SP6GK/ADF4351-LO-module/Photos/IMG_20250809_144723.jpg

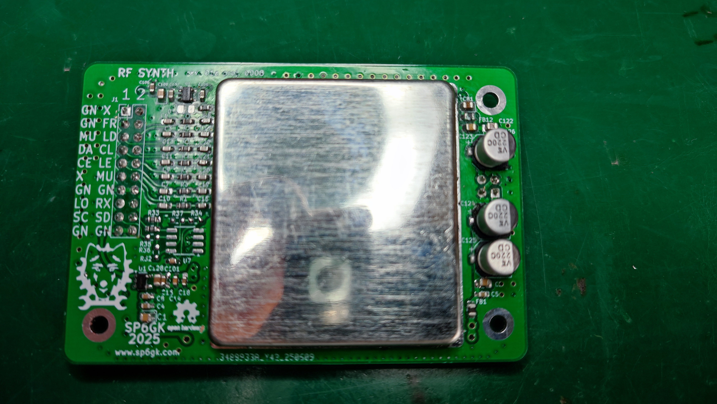
Photos/IMG_20250809_144723.jpg
