SP6GK/ADF4351-LO-module/Verification/Measurements/Adf4351_400MHz_Harmonics.png

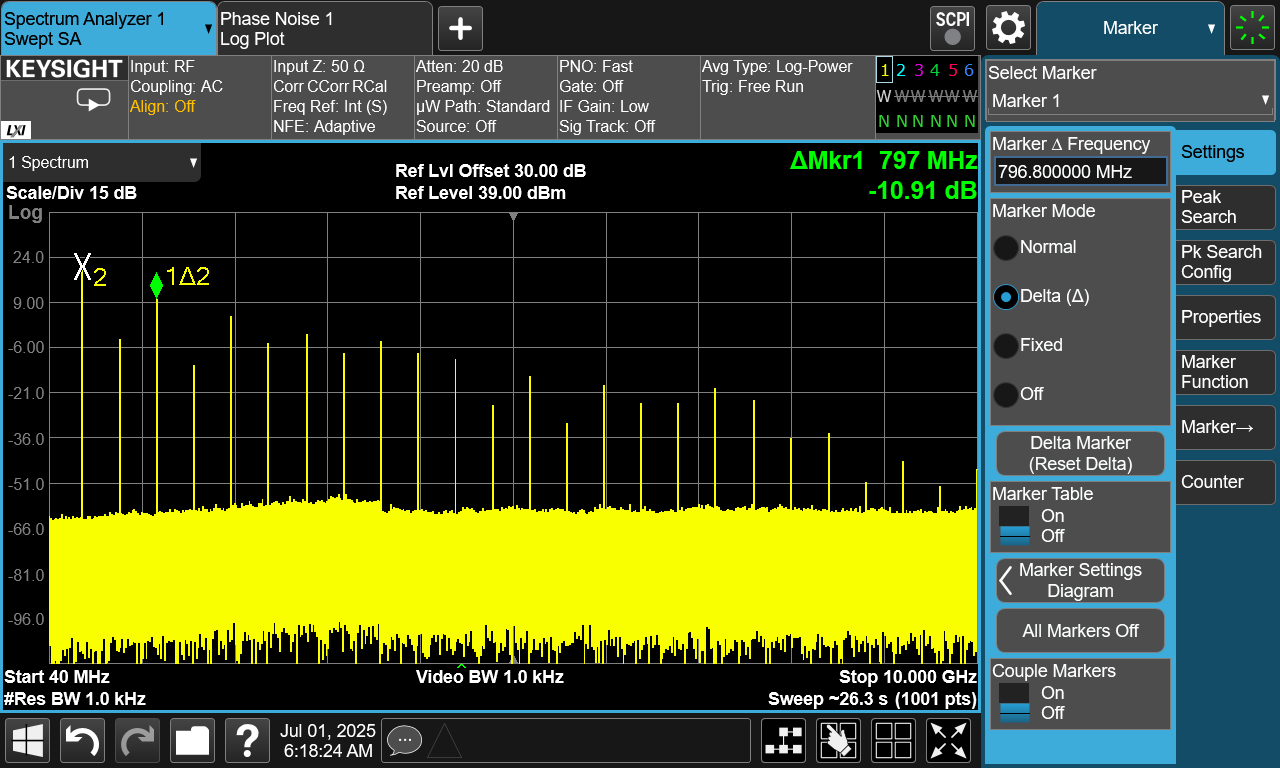
Verification/Measurements/Adf4351_400MHz_Harmonics.png
