SP6GK/ADF4351-LO-module/Verification/Measurements/Adf4351_2400MHz_narrow_0000.png

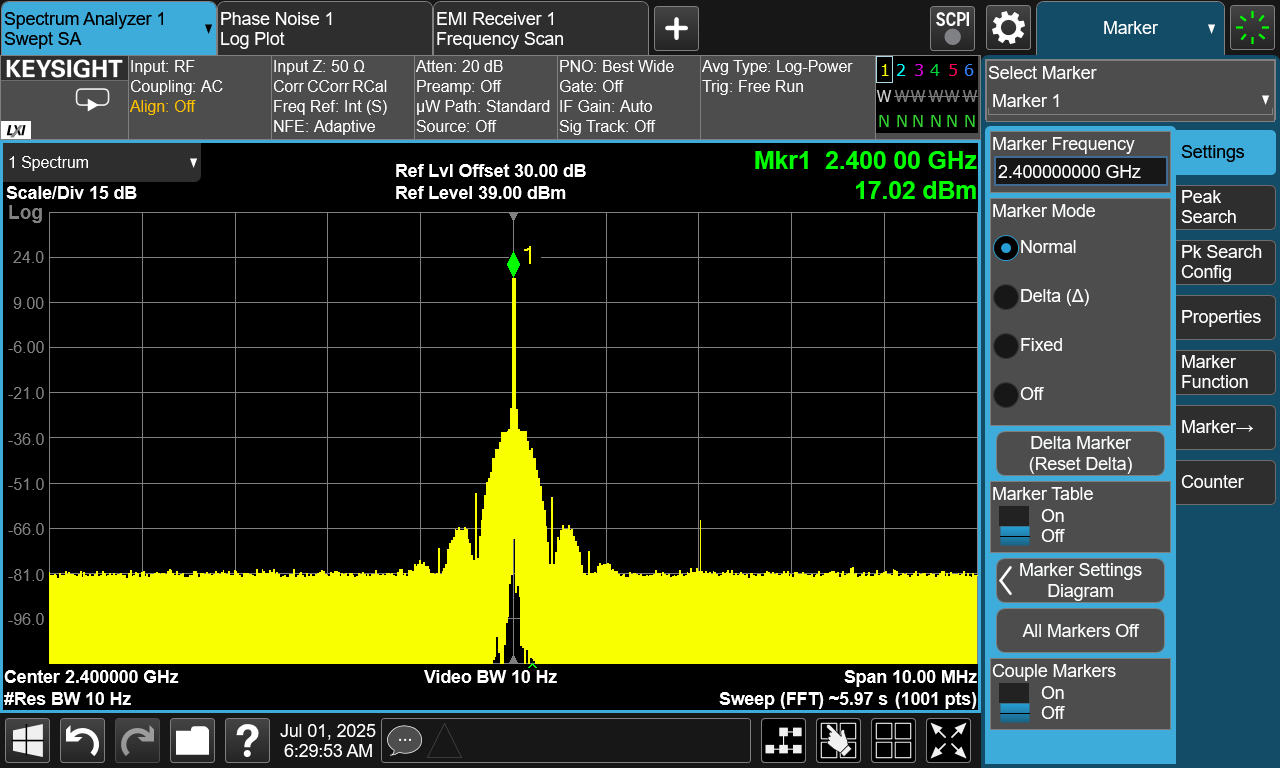
Verification/Measurements/Adf4351_2400MHz_narrow_0000.png
